Einstellung/Bionic-Robot/BionicRobot/六足机器人模型(未使用)/模型/底盘_下_2.SLDPRT

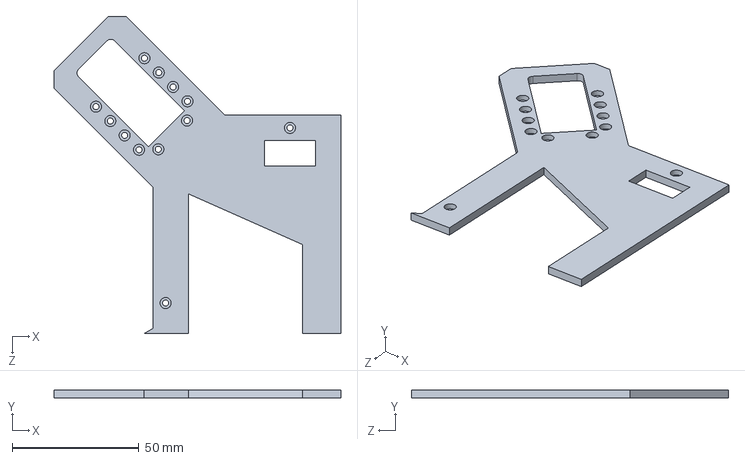
[picture p45: CAD file, 2019-01-06]
BionicRobot/六足机器人模型(未使用)/模型/底盘_下_2.SLDPRT
112.9 x 3.00 x 124.9 mm
