Einstellung/Bionic-Robot/BionicRobot/机器人结构/零件1.SLDPRT

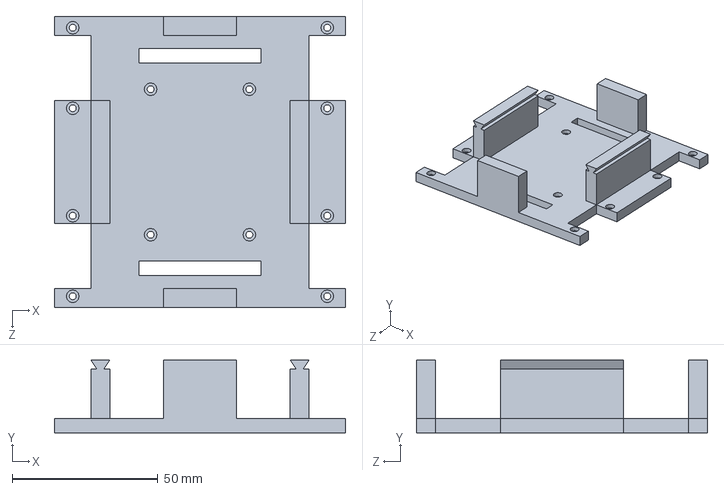
[picture p46: CAD file, 2019-01-06]
BionicRobot/机器人结构/零件1.SLDPRT
100.0 x 25.0 x 100.0 mm
