Einstellung/Bionic-Robot/BionicRobot/机器人结构/舵盘.SLDPRT

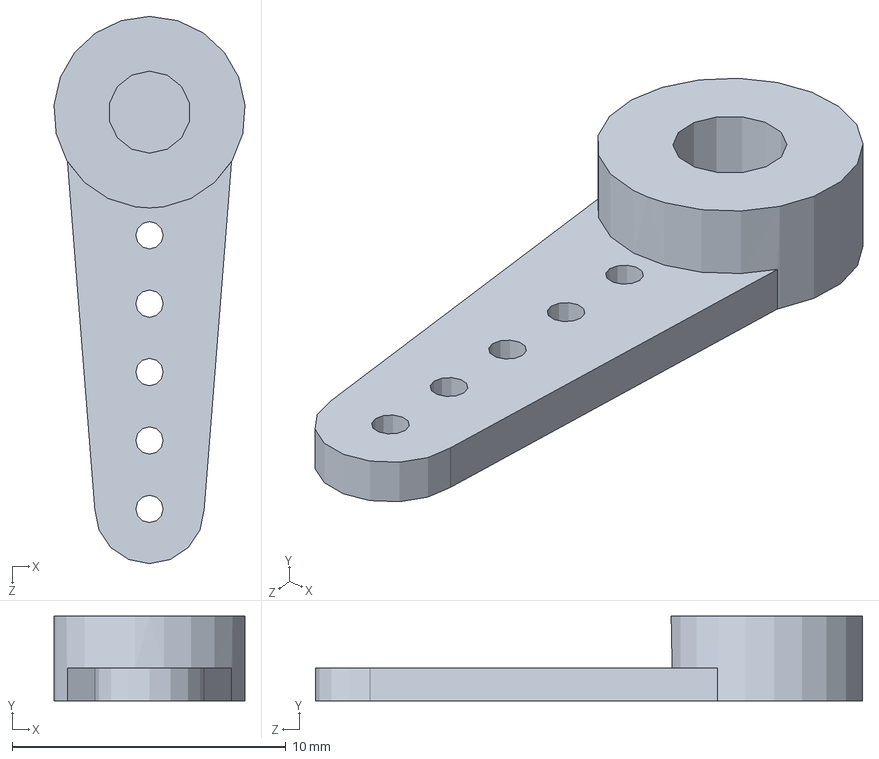
[picture p47: CAD file, 2019-01-06]
BionicRobot/机器人结构/舵盘.SLDPRT
6.98 x 3.10 x 20.0 mm
