Einstellung/Bionic-Robot/BionicRobot/机器人结构/SG90舵机.SLDPRT

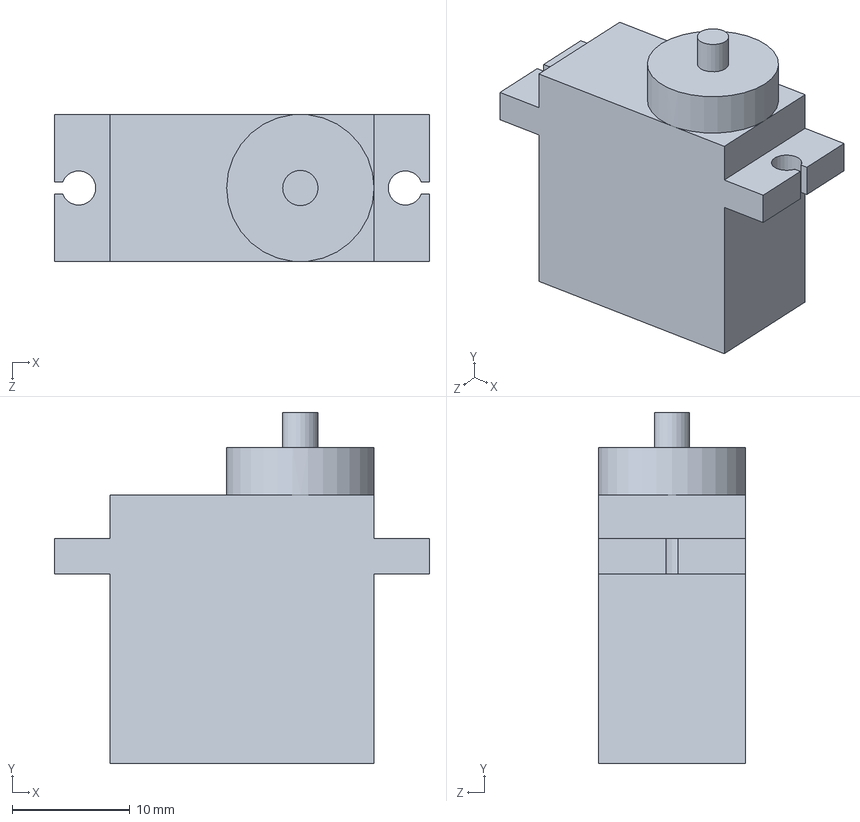
[picture p48: CAD file, 2019-01-06]
BionicRobot/机器人结构/SG90舵机.SLDPRT
31.8 x 29.8 x 12.5 mm
