Einstellung/Bionic-Robot/BionicRobot/六足机器人模型(未使用)/模型/底盘_下_新.SLDPRT

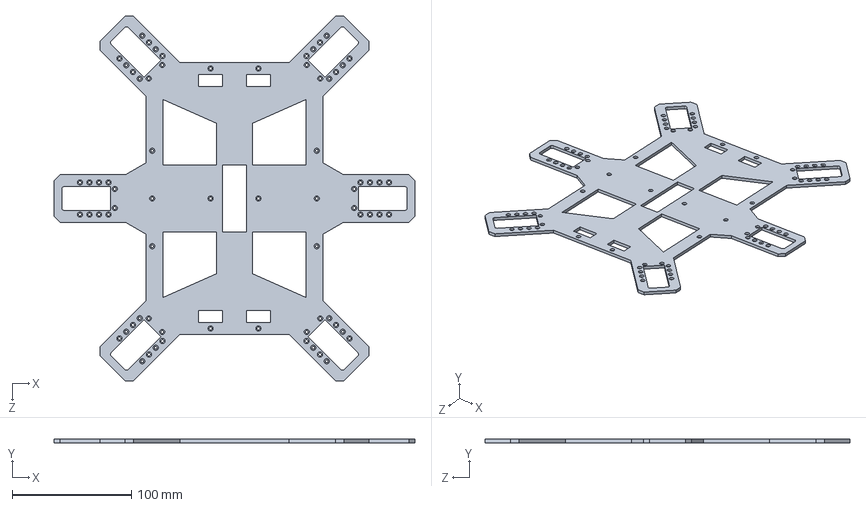
[picture p49: CAD file, 2019-01-06]
BionicRobot/六足机器人模型(未使用)/模型/底盘_下_新.SLDPRT
302.6 x 3.00 x 305.8 mm
