Einstellung/Bionic-Robot/BionicRobot/机器人结构/脚.SLDPRT

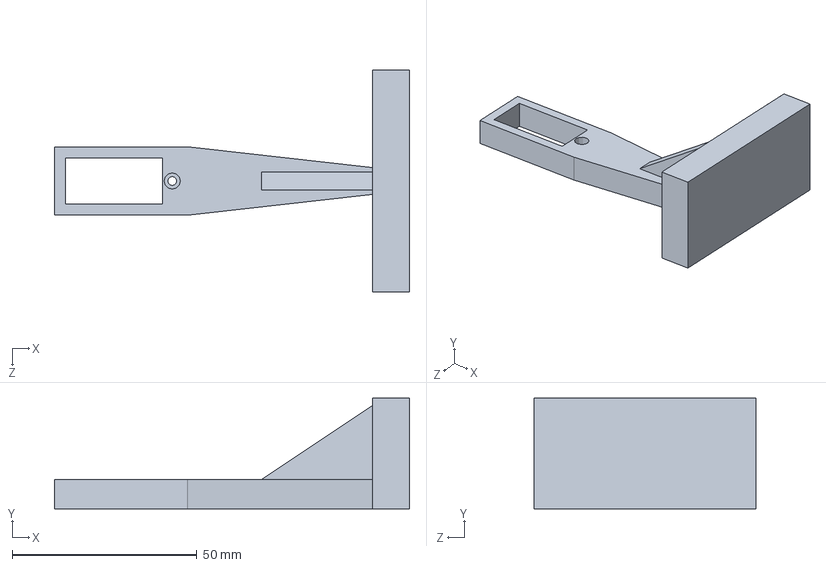
[picture p50: CAD file, 2019-01-06]
BionicRobot/机器人结构/脚.SLDPRT
96.0 x 30.0 x 60.0 mm
