Einstellung/Bionic-Robot/BionicRobot/六足机器人模型(未使用)/模型/舵机壳下.SLDPRT

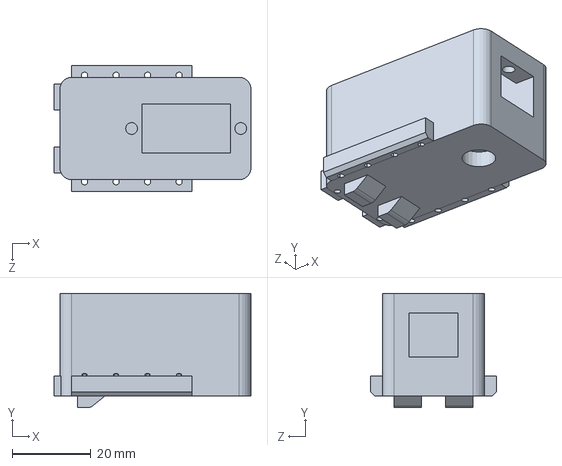
[picture p51: CAD file, 2019-01-06]
BionicRobot/六足机器人模型(未使用)/模型/舵机壳下.SLDPRT
50.0 x 29.0 x 32.0 mm
