Einstellung/Bionic-Robot/BionicRobot/六足机器人模型(未使用)/模型/关节1_螺母_新.SLDPRT

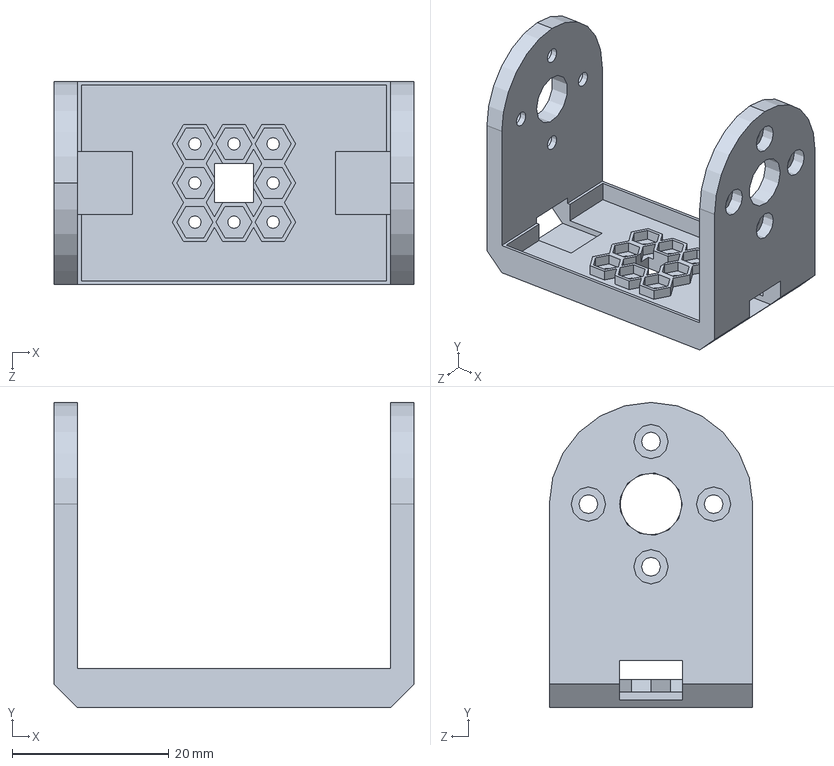
[picture p53: CAD file, 2019-01-06]
BionicRobot/六足机器人模型(未使用)/模型/关节1_螺母_新.SLDPRT
46.0 x 39.0 x 26.0 mm
