Einstellung/Bionic-Robot/BionicRobot/机器人结构/机身.SLDPRT

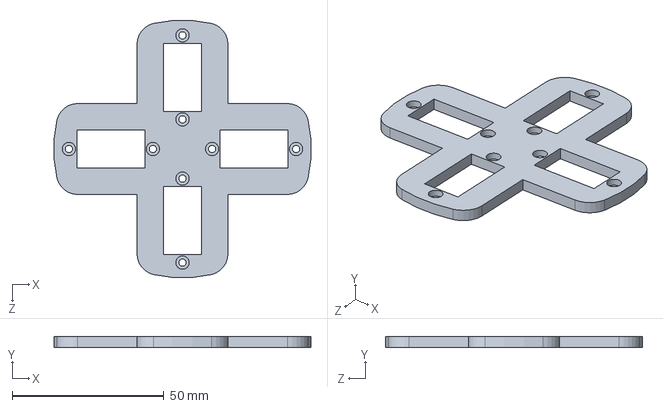
[picture p54: CAD file, 2019-01-06]
BionicRobot/机器人结构/机身.SLDPRT
84.8 x 3.50 x 84.8 mm
