Einstellung/Bionic-Robot/BionicRobot/六足机器人模型(未使用)/模型/足.SLDPRT

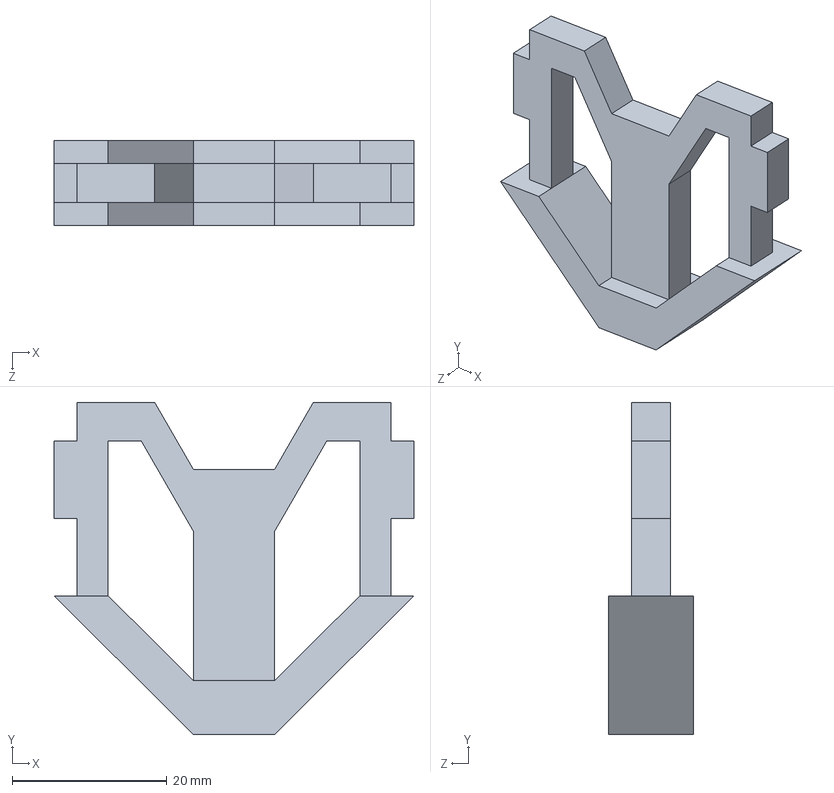
[picture p55: CAD file, 2019-01-06]
BionicRobot/六足机器人模型(未使用)/模型/足.SLDPRT
46.5 x 42.9 x 11.0 mm
