Einstellung/Bionic-Robot/BionicRobot/机器人结构/零件2.SLDPRT

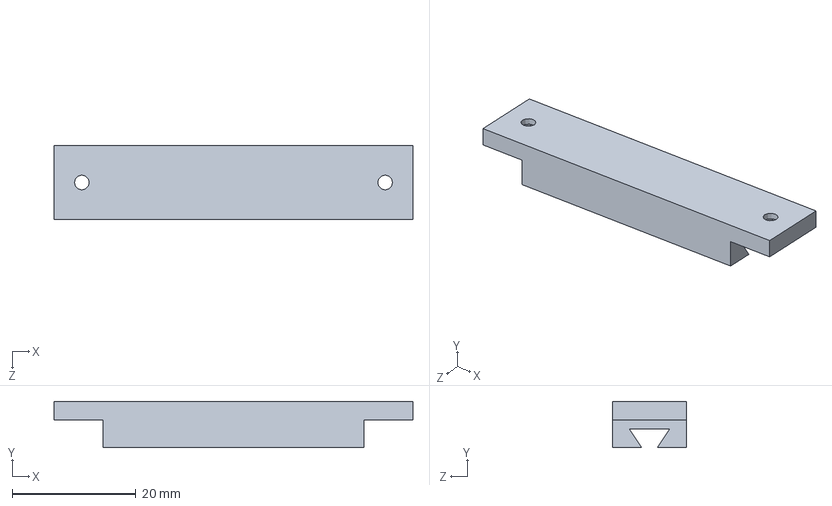
[picture p56: CAD file, 2019-01-06]
BionicRobot/机器人结构/零件2.SLDPRT
58.0 x 7.50 x 12.0 mm
