Einstellung/Bionic-Robot/BionicRobot/六足机器人模型(未使用)/模型/关节2_螺丝.SLDPRT

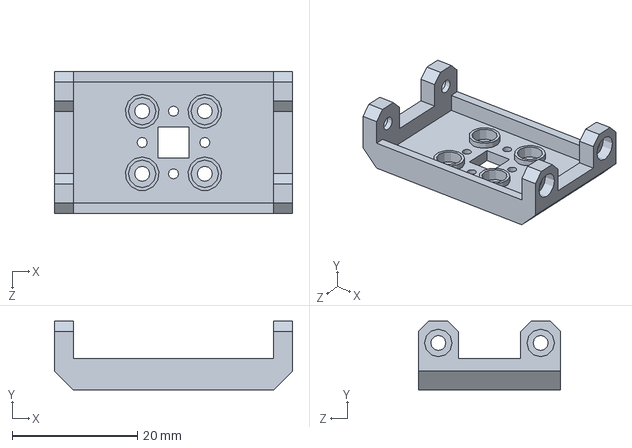
[picture p57: CAD file, 2019-01-06]
BionicRobot/六足机器人模型(未使用)/模型/关节2_螺丝.SLDPRT
38.0 x 11.0 x 22.8 mm
