Einstellung/Bionic-Robot/BionicRobot/机器人结构/平台.SLDPRT

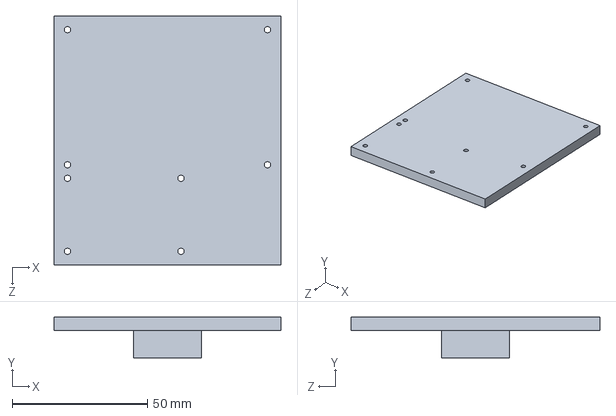
[picture p58: CAD file, 2019-01-06]
BionicRobot/机器人结构/平台.SLDPRT
84.0 x 15.0 x 92.0 mm
