Einstellung/Bionic-Robot/BionicRobot/六足机器人模型(未使用)/模型/底盘支撑 _2.SLDPRT

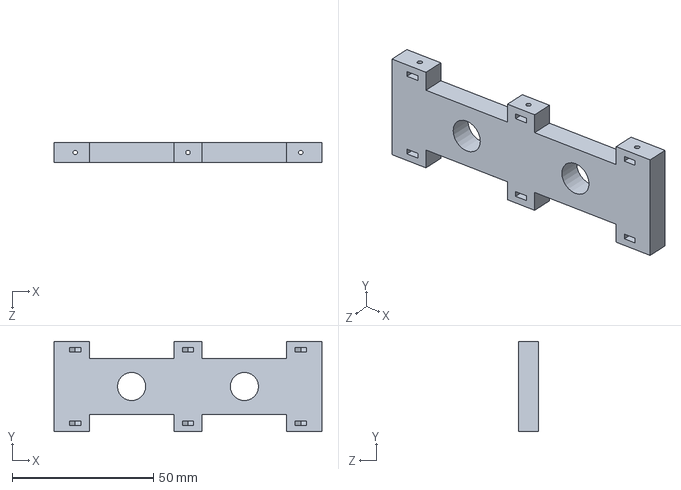
[picture p60: CAD file, 2019-01-06]
BionicRobot/六足机器人模型(未使用)/模型/底盘支撑 _2.SLDPRT
95.0 x 32.0 x 7.00 mm
