Einstellung/Bionic-Robot/BionicRobot/六足机器人模型(未使用)/模型/腿 - 1.SLDPRT

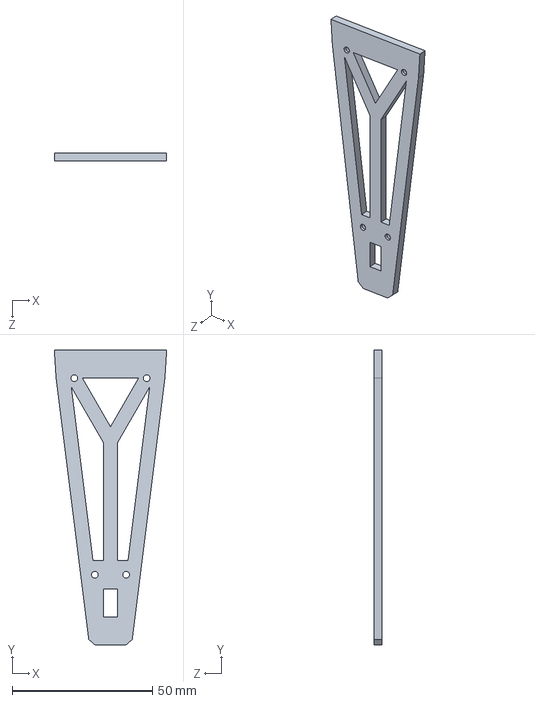
[picture p63: CAD file, 2019-01-06]
BionicRobot/六足机器人模型(未使用)/模型/腿 - 1.SLDPRT
40.0 x 105.0 x 3.00 mm
