Einstellung/Bionic-Robot/BionicRobot/六足机器人模型(未使用)/模型/舵机零件.SLDPRT

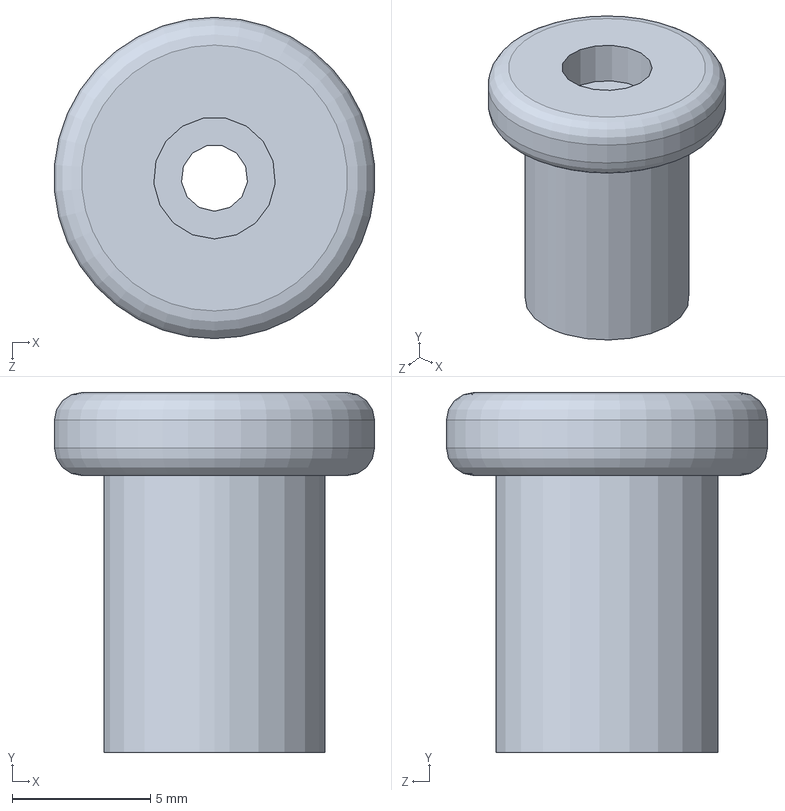
[picture p68: CAD file, 2019-01-06]
BionicRobot/六足机器人模型(未使用)/模型/舵机零件.SLDPRT
11.6 x 13.0 x 11.6 mm
