Einstellung/Bionic-Robot/BionicRobot/六足机器人模型(未使用)/模型/关节1_螺丝.SLDPRT

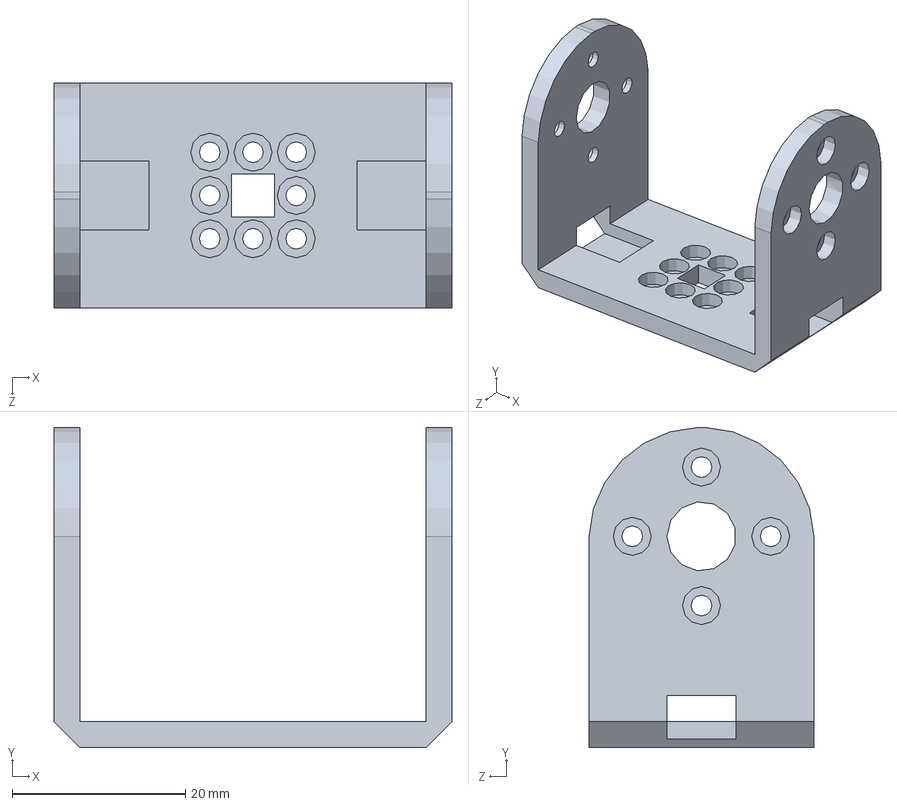
[picture p70: CAD file, 2019-01-06]
BionicRobot/六足机器人模型(未使用)/模型/关节1_螺丝.SLDPRT
46.0 x 37.0 x 26.0 mm
